awgraves/stm32_photo_viewer/src/mcu/registers.h

#pragma once

#include <stdint.h>

#define BIT(n) (1U << (n))

/*
   Systick info comes from Arm Cortex M4 general user guide pg. 249

   For SYS_CRS values:
   bit 2 set: set clock source as internal CPU clock
   bit 1 set: enable Systick IRQ
   bit 0 set: enable the counter
*/
#define SYSTICK_BASE (0xE000E010)
#define SYSTICK_CSR_BITS (BIT(2) | BIT(1) | BIT(0))

typedef struct {
  volatile uint32_t CSR;
  volatile uint32_t RVR;
  volatile uint32_t CVR;
  volatile uint32_t CALIB;
} SYSTICK_t;

#define SYSTICK ((SYSTICK_t *const)SYSTICK_BASE)

// RM0390 pg. 170
typedef struct {
  volatile uint32_t CR, PLLCFGR, CFGR, _unused_1[9], AHB1ENR, _unused_2[3],
      APB1ENR, APB2ENR, _unused_3[20];
} RCC_t;

// RM0390 pg. 57
#define RCC_BASE (0x40023800UL)
#define RCC ((RCC_t *const)RCC_BASE)

// RM0390 pg. 127 - 128
#define RCC_CR_PLLRDY (BIT(25))
#define RCC_CR_PLLON (BIT(24))
#define RCC_CR_HSIRDY (BIT(1))
#define RCC_CR_HSION (BIT(0))

// RM0390 pg. 129
typedef enum {
  RCC_PLLP_DIV_2,
  RCC_PLLP_DIV_4,
  RCC_PLLP_DIV_6,
  RCC_PLLP_DIV_8
} PLLP_divisor_t;
#define RCC_PLLCFGR_PLLP(divisor) ((divisor & 0x3) << 16)
#define RCC_PLLCFGR_PLLN(multiplier) ((multiplier & 0x1FF) << 6)
#define RCC_PLLCFGR_PLLM(divisor) ((divisor & 0x3F) << 0)
#define RCC_PLLCFGR_PLLQ(divisor) ((divisor & 0xF) << 24)

// RM0390 pg. 132
typedef enum { RCC_SRC_HSI, RCC_SRC_HSE, RCC_SRC_PLL, RCC_SRC_PLLR } rcc_src_t;
#define RCC_CFGR_SWS(src) ((src & 0x3) << 2)
#define RCC_CFGR_SW(src) ((src & 0x3) << 0)

// RM 0390 pg. 132
typedef enum {
  APB_PRESCALER_NONE = 0b0,
  APB_PRESCALER_DIV_2 = 0b100,
  APB_PRESCALER_DIV_4 = 0b101,
  APB_PRESCALER_DIV_8 = 0b110,
  APB_PRESCALER_DIV_16 = 0b111
} apb_prescaler_t;
#define RCC_CFGR_APB1_PRESCALE(prescaler) ((prescaler & 0x7) << 10)
#define RCC_CFGR_APB2_PRESCALE(prescaler) ((prescaler & 0x7) << 13)

// RM0390 pg.143
#define RCC_AHB1ENR_GPIOA (BIT(0))
#define RCC_AHB1ENR_DMA2 (BIT(22))

// RM0390 pg. 148
#define RCC_APB1ENR_TIM2 (BIT(0))

// RM0390 pg. 148
#define RCC_APB2ENR_SPI1 (BIT(12))
#define RCC_APB2ENR_SYSCFG (BIT(14))
#define RCC_APB2ENR_SDIO (BIT(11))
#define RCC_APB2ENR_TIM1 (BIT(0))

// RM0390 pg. 87
typedef struct {
  volatile uint32_t ACR, KEYR, OPTKEYR, SR, CR, OPTCR;
} FLASH_t;

#define FLASH_BASE (0x40023C00UL)
#define FLASH ((FLASH_t *const)FLASH_BASE)

#define FLASH_ACR_ICEN (BIT(9))
#define FLASH_ACR_PRFTEN (BIT(8))
#define FLASH_ACR_LATENCY_0 (0x0)
#define FLASH_ACR_LATENCY_1 (0x1)
#define FLASH_ACR_LATENCY_2 (0x2)
#define FLASH_ACR_LATENCY_3 (0x3)
#define FLASH_ACR_LATENCY_5 (0x5)

// RM0390 pg. 191
// struct total 4 bytes (32 bit) x 10 fields = 40 bytes
// but each range per PORT (RM0390 pg. 58) is 0x400 large = 1024 bytes
// so each GPIOA, B, C.. is padded with 1024 - 40 = 984 additional bytes
typedef struct {
  volatile uint32_t MODER, OTYPER, OSPEEDER, PUPDR, IDR, ODR, BSRR, LCKR, AFRL,
      AFRH;
} GPIO_t;

#define GPIOx_BASE (0x40020000UL)
#define GPIO_PORT_OFFSET (0x400U)

// SPI register map RM0390 pg. 874
typedef struct {
  volatile uint32_t CR1, CR2, SR, DR, CRCPR, RXCRCR, TXCRCR, _unused[2];
} SPI_t;

// CR1
#define SPI_CR1_ENABLE (BIT(6))
#define SPI_CR1_MASTER (BIT(2))
#define SPI_CR1_SSM (BIT(9))
#define SPI_CR1_SSI (BIT(8))

// CR2
#define SPI_CR2_TXDMAEN (BIT(1))

// SR
#define SPI_SR_BSY (BIT(7))
#define SPI_SR_TXE (BIT(1))
#define SPI_SR_RXNE (BIT(0))

// on APB2 bus
#define SPI1_BASE (0x40013000UL)
#define SPI1 ((SPI_t *const)SPI1_BASE)

// RM0390 pg. 231
typedef struct {
  volatile uint32_t CR, NDTR, PAR, M0AR, M1AR, FCR;
} DMA_stream_t;

// RM0390 pg. 231
typedef struct {
  volatile uint32_t LISR, HISR, LIFCR, HIFCR;

  DMA_stream_t STREAM[8];
} DMA_t;

// DMA_LISR pg. 222
#define DMA_LISR_STREAM_3_TCIF (BIT(27)) // signals xfer complete
// DMA_HISR pg. 223
#define DMA_HISR_STREAM_6_TCIF (BIT(21))

// DMA_LIFCR pg. 224
#define DMA_LIFCR_STREAM_3_ALL_FLAGS (0xFU << 24)
// DMA_HIFCR pg. 224
#define DMA_HIFCR_STREAM_6_ALL_FLAGS (0xFU << 18)

// DMA_SxCR pg. 225
#define DMA_SxCR_CHSEL_3 (0x3U << 25)
#define DMA_SxCR_CHSEL_4 (0x4U << 25)
#define DMA_SxCR_MBURST_4_BEATS (0x1 << 23)
#define DMA_SxCR_PBURST_4_BEATS (0x1 << 21)
// pg. 226
#define DMA_SxCR_MSIZE_WORD (0x2U << 13)
#define DMA_SxCR_PSIZE_WORD (0x2U << 11)
#define DMA_SxCR_INCR_MEM (BIT(10))
// pg. 227
#define DMA_SxCR_DIR_MEM_TO_PERIPH (0x1U << 6)
#define DMA_SxCR_DIR_PERIPH_TO_MEM (0x0U << 6)
#define DMA_SxCR_PERIPH_CONTROLS_FLOW (BIT(5))
// pg. 228
#define DMA_SxCR_EN (BIT(0)) // cleared by hardware when DMA end of xfer

// pg. 230 FIFO control register
#define DMA_SxFCR_DMDIS (BIT(2)) // direct mode disable
#define DMA_SxFCR_FIFO_THRESHOLD_FULL (0x3U)

// pg. 58
#define DMA2_BASE (0x40026400)
#define DMA2 ((DMA_t *const)DMA2_BASE)

// pg. 246
typedef struct {
  volatile uint32_t IMR, EMR, RTSR, FTSR, SWIER, PR;
} EXTI_t;

// pg. 58
#define EXTI_BASE (0x40013C00UL)
#define EXTI ((EXTI_t *const)EXTI_BASE)

// pg. 199
typedef struct {
  volatile uint32_t MEMRMP, PMC, EXTICR[4], CMPCR, CFGR;
} SYSCFG_t;

// pg. 58
#define SYSCF_BASE (0x40013800UL)
#define SYSCF ((SYSCFG_t *const)SYSCF_BASE)

// pg. 195
#define SYSCFG_EXTI_INPUT_PA 0x0000U
#define SYSCFG_EXTI_INPUT_MASK(exti_pos, input) ((input) << (exti_pos * 4))

/*
ARM Cortex M4 general user manual pg. 233
*/
typedef struct {
  volatile uint32_t ISER; // 'Interrupt set-enable registers'
  // ... more registers exist, but not using them.
  /*
  Note: just need ISER 0.
  In RM 0390 pg. 236, the ISER bit to set corresponds to the 'position' col
  for EXTI0 - EXTI4, these are 6 - 10 respectively
  */
} NVIC_t;

// NOTE: this will break if pinno > 4
#define NVIC_EXTI_BIT_FROM_PINNO(pinno) (BIT(pinno + 6))

#define NVIC_BASE 0xE000E100UL
#define NVIC ((NVIC_t *const)NVIC_BASE)

// General purpose (GP) and advanced (ADV) timers
// share their initial ordering
typedef struct {
  volatile uint32_t CR1, CR2, SMCR, DIER, SR, EGR, CCMR1, CCMR2, CCER, CNT, PSC,
      ARR;
} TIM_COMMON_t;

// RM 0390 pg. 569, General Purpose
typedef struct {
  TIM_COMMON_t common;
  volatile uint32_t CCR1, CCR2, CCR3, CCR4, DCR, DMAR, OR;
} TIM_GP_t;

// RM 0390 pg. 59, on APB1 bus
#define TIM2_BASE (0x40000000UL)
#define TIM2 ((TIM_GP_t *const)TIM2_BASE)

// RM 0390 pg. 566, (advanced control timer)
typedef struct {
  TIM_COMMON_t common;
  volatile uint32_t RCR, CCR1, CCR2, CCR3, CCR4, BDTR, DCR, DMAR;
} TIM_ADV_t;

// RM 0390 pg. 58, on APB2 bus
#define TIM1_BASE (0x40010000)
#define TIM1 ((TIM_ADV_t *const)TIM1_BASE)

// RM0390 pg. 548 (control reg1)
// auto-reload preload enable
#define TIMx_CR1_ARPE (BIT(7))
#define TIMx_CR1_CEN (BIT(0))

// RM0390 pg. 552 (slave mode control)
#define TIMx_SMCR_SMS_T1_EDGE_TRIGGERS (0x2U)
#define TIMx_SMCR_SMS_BOTH_EDGES_TRIGGER (0x3U)
// RM0390 pg. 557 - 558 (capture/compare mode register)
// input capture 1 and 2 filters
#define TIMx_CCMR1_IC2F_4_SAMPLES ((0x2) << 12)
#define TIMx_CCMR1_IC1F_4_SAMPLES ((0x2) << 4)

#define TIMx_CCMR2_OC4M_PWM_MODE_1 ((0x6) << 12)
#define TIMx_CCMR2_OC4PE (BIT(11))

// RM0390 pg. 562 (capture/compare enable)
#define TIMx_CCER_CC1_ACTIVE_LOW (BIT(1))
#define TIMx_CCER_CC2_ACTIVE_LOW (BIT(5))
#define TIMx_CCER_CC1_EN (BIT(0))
#define TIMx_CCER_CC2_EN (BIT(4))
#define TIMx_CCER_CC4_EN (BIT(12))

// RM0390 pg. 493
// forces an update generation
#define TIMx_EGR_UG (BIT(0))

// Advanced timers require main output enable
#define TIM_ADV_BDTR_MOE (BIT(15))

// RM 0390 pg. 1016, APB2 bus
typedef struct {
  volatile uint32_t POWER, CLKCR, ARG, CMD, RESPCMD, RESP1, RESP2, RESP3, RESP4,
      DTIMER, DLEN, DCTRL, DCOUNT, STA, ICR, MASK;
  volatile uint32_t _reserved[2];   // 0x40, 0x44
  volatile uint32_t FIFOCNT;        // 0x48
  volatile uint32_t _reserved2[13]; // 0x4C to 0x7C
  volatile uint32_t FIFO;           // 0x80 (0x40012C80)
} SDIO_t;

// RM 0390 pg. 58, aka SDMMC
#define SDIO_BASE (0x40012C00UL)
#define SDIO ((SDIO_t *const)SDIO_BASE)

// RM 0390 pg. 1002
#define SDIO_POWER_OFF (0x00U)
#define SDIO_POWER_ON (0x3U)

/*
   RM 0390 pg. 1003
   SDIO_CLK == the STM32 clock (PLL48Mhz) that feeds the internal SDIO periph
   SDIO_CK == actual output to SD card over CLK line

   SDIO_CK = SDIOCLK / [CLKDIV + 2] note: only even CLKDIV values allowed
   except if BYPASS bit is set, then SDIO_CK = SDIO_CLK

   During identification mode, SDIO_CK must be less than 400 kHz.
   afterwards, when RCAs are assigned, can increase bus freq.
*/
#define SDIO_CLKCR_BUS_WIDTH(width) ((width & 0x3) << 11)
#define SDIO_CLKCR_BUS_WIDTH_CLEAR_BITS (0x3U << 11)
#define SDIO_CLKCR_BYPASS (BIT(10))
#define SDIO_CLKCR_PWRSAV (BIT(9)) // automatically turn off clock when bus idle
#define SDIO_CLKCR_CLKEN (BIT(8))
#define SDIO_CLKCR_CLKDIV_CLEAR (0xFFU)

// RM 0390 pg. 1004
#define SDIO_CMD_CPSMEN (BIT(10)) // starts the command path state machine
#define SDIO_CMD_WAIT_RESP_NONE ((0x0U) << 6)
#define SDIO_CMD_WAIT_RESP_SHORT ((0x1U) << 6)
#define SDIO_CMD_WAIT_RESP_LONG ((0x3U) << 6)

// RM 0390 pg. 1008
// note value in SDIO_DLEN is a multiple of the block size SDMMC_DCTRL, ie 512
// bytes
#define SDIO_DCTRL_DBLOCKSIZE_512 ((0x9U) << 4)
#define SDIO_DCTRL_DMAEN (BIT(3))
#define SDIO_DCTRL_DTDIR_FROM_CARD_TO_CONTROLLER (BIT(1))
#define SDIO_DCTRL_DTEN (BIT(0))

// RM 0390 pg. 1009 - 1010
#define SDIO_STA_RXDAVL (BIT(21))   // data is available
#define SDIO_STA_RXFIFOE (BIT(19))  // all data read
#define SDIO_STA_RXFIFOHF (BIT(15)) // at least 8 words in FIFO
#define SDIO_STA_RXACT (BIT(13))    // data receive in progress
#define SDIO_STA_TXACT (BIT(12))    // data transmit in progress
#define SDIO_STA_CMDACT (BIT(11))   // command xfer in progress
#define SDIO_STA_DBCKEND (BIT(10))  // block sent/received (CRC check pass)
#define SDIO_STA_DATAEND (BIT(8))   // data end (data counter is zero)
#define SDIO_STA_CMDSENT (BIT(7))   // command sent (no response required)
#define SDIO_STA_CMDREND                                                       \
  (BIT(6)) // command response received (CRC check passed)
#define SDIO_STA_RXOVERR (BIT(5))  // FIFO overrun error
#define SDIO_STA_TXUNDERR (BIT(4)) // FIFO underrun error
#define SDIO_STA_DTIMEOUT (BIT(3)) // data resp timeout
#define SDIO_STA_CTIMEOUT (BIT(2)) // command resp timeout
#define SDIO_STA_DCRCFAIL (BIT(1)) // block sent/received (CRC check fail)
#define SDIO_STA_CCRCFAIL (BIT(0)) // command resp received, but CRC check fail

// RM 0390 pg. 1011 (clears corresponding flags in STA register)
#define SDIO_ICR_DBCKENDC (BIT(10))
#define SDIO_ICR_DATAENDC (BIT(8))
#define SDIO_ICR_CMDSENTC (BIT(7))
#define SDIO_ICR_CMDRENDC (BIT(6))
#define SDIO_ICR_RXOVERRC (BIT(5))
#define SDIO_ICR_TXUNDERRC (BIT(4))
#define SDIO_ICR_DTIMEOUTC (BIT(3))
#define SDIO_ICR_CTIMEOUTC (BIT(2))
#define SDIO_ICR_DCRCFAILC (BIT(1))
#define SDIO_ICR_CCRCFAILC (BIT(0))
